PhunderDev/Numpad-V2.0/Photos/1.jpeg

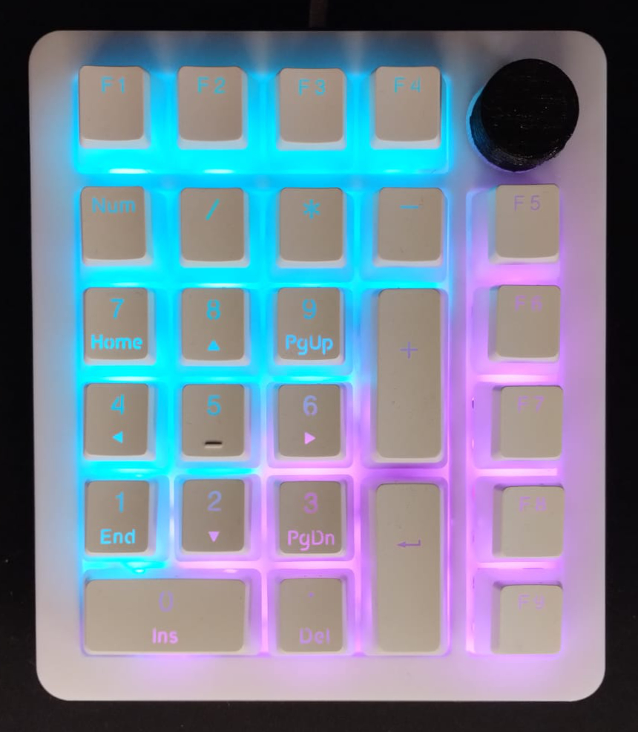
Photos/1.jpeg
