PhunderDev/Numpad-V2.0/Photos/4.jpeg

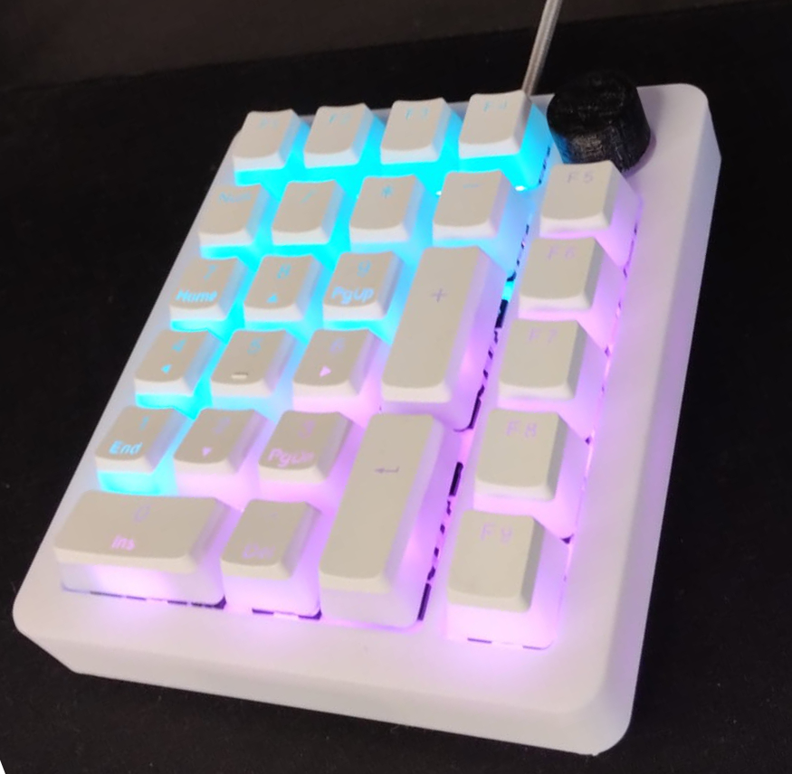
Photos/4.jpeg
